peter-tanner/TREX-laser-transmit-receive-PCB/Simulation/Receiver/AAA_reverse_bias_sim.asc

C1: cap; 4.7µ
C2: cap; 10p
C3: cap; 1µ
C4: cap; 4.7µ
C5: cap; 1µ
D1: diode; MBR0530L
D2: diode; MBR0530L
D3: diode; MBR0530L
I1: current; PULSE(0 50u 1n 1n 1n 1G)
I2: current; PULSE(0 50u 1n 1n 1n 1G)
L1: ind; 10µ
R1: res; 200k
R2: res; 2Meg
U1: TPS61040_TRANS
V1: voltage; 5
Named nets: 0, -13V, +13V
.tran 1.2m
USE NORMAL
SIMULATOR
(NOT ALTERNATIVE)
50uA PD load
