peter-tanner/TREX-laser-transmit-receive-PCB/Simulation/Receiver/AAA_LMH34400_Sim.asc

C1: cap; 11p
DC_Noise: current; 5µ
PD: current; PULSE(500u 0 0 5n 5n 0 40n)
R1: res; 27k
R2: res; 5.6k
R3: res; 51
U1: TLV3601
U2: SN74LVC1G14
U4: LMH34400
V1: voltage; 3.3
V3: voltage; 3.3
Named nets: 0, Digital_OUT
.tran 0 1.5u 1u
RUN `download-copyrighted-libraries.sh`
TO DOWNLOAD SPICE MODELS BEFORE
RUNNING FIRST SIMULATION
 
AGNI
