peter-tanner/TREX-laser-transmit-receive-PCB/Simulation/Transmitter/AAA_transmitter_laser_driver_simulation.asc

C1: cap; 100n
C2: cap; 100n
C3: cap; 1µ
C4: cap; 1p
D1: LED; PT-121-B
D3: TVSdiode; SMBJ24CA
D4: TVSdiode; SMBJ24CA
Q1: npn; 2SC3356
Q2: npn; 2SC3356
R1: res; 1
R4: res; 47
R7: res; 27
R8: res; 900
R9: res; 100
U1: OPA355
U2: OPA355
U3: SN74AUC1G66
U4: SN74AUC1G66
V1: voltage; 3.3
V3: voltage; .12
V4: voltage; 3
V5: voltage; 5
V6: voltage; PULSE(3 0 0 1n 1n 9n 20n)
V7: voltage; PULSE(0 3 0 1n 1n 9n 20n)
Named nets: 0, VCC, 3V0
.tran 0 100n 0 1p
.param X=10n
.step param X list 1n 2n 5n 10n
.step param C list 10p 100p 1n 10n
Recommendation 1: Select OPA355 (OPA355UA/2K5)
* High input impedance
* High GBW (200 MegHz)
 
Recommendation 2: Use 2SC3356 NPN
* Very cheap (basic parts)
* 7GHz switching speed
* Spice model from https://pcb.mit.edu/labs/lab_03/
.model 2SC3356 NPN(IS=6E-16 NF=0.98 ISE=32E-16 NE=1.93 BF=120 
+IKF=0.0.17 VAF=10 NR=0.991 ISC=0 NC=2 BR=12 IKR=0.17 VAR=3.9 
+RB=4.16 IRB=1.96E-04 RBM=3.6 RE=0.38 RC=2  XTB=0 EG=1.11 XTI=3 
+CJE=2.8E-12 VJE=1.3 MJE=0.5 TF=15E-12 XTF=6 VTF=10 ITF=0.2 PTF=0 
+CJC=1.1E-12 VJC=0.7 MJC=0.55 XCJC=0.3 TR=1E-09 CJS=0 VJS=0.75 
+MJS=0 FC=0.5 Vceo=12 Icrating=100m mfg=cel)
Add level shifter here, use 3V max for RF transistors
No spice model for SPDT sn74auc2g53 - use two switches
careful of make before break behavior
bias
modulation
RUN `download-copyrighted-libraries.sh`
TO DOWNLOAD SPICE MODELS BEFORE
RUNNING FIRST SIMULATION
 
PETERUS
bias: 4.5mA
modulating: 7.2mA
adjust potentiometer
