peter-tanner/TREX-laser-transmit-receive-PCB/Simulation/Transmitter/AAA_transmitter_laser_driver_simulation_esd_protection.asc

C1: cap; 100n
C2: cap; 100n
C3: cap; 20p
C4: cap; 110p
C5: cap; 20p
C6: cap; 15p
C7: cap; 5p
D1: LED; PT-121-B
D3: TVSdiode; SMCJ33A
D4: TVSdiode; SMBJ24CA
L1: ind; 6n
L2: ind; 3500n
L3: FerriteBead; 1.38µ; Ipk=1 Rser=0.2 Rpar=813 Cpar=617f mfg="Würth Elektronik" pn="742792651 WE-CBF 0603"
Q1: npn; 2SC3356
Q2: npn; 2SC3356
R1: res; 330
R2: res; 120
R3: res; 36
R4: res; 47
R5: res; 36
R7: res; 27
R8: res; 90
R9: res; 10
R11: res; 100
S1: sw; SW1
U1: OPA355
U2: OPA355
V1: voltage; 3.3
V3: voltage; .12
V4: voltage; 3
V5: voltage; 5
V6: voltage; PWL(0 0 10E-9 0 10.01E-9 1)
V7: voltage; PULSE(0 3 0 1n 1n 9n 20n)
Named nets: 0, VCC, 3V0, ESD_OUT, ESD_CAP, ESD_SW
.tran 150n
Recommendation 1: Select OPA355 (OPA355UA/2K5)
* High input impedance
* High GBW (200 MegHz)
 
Recommendation 2: Use 2SC3356 NPN
* Very cheap (basic parts)
* 7GHz switching speed
* Spice model from https://pcb.mit.edu/labs/lab_03/
.model 2SC3356 NPN(IS=6E-16 NF=0.98 ISE=32E-16 NE=1.93 BF=120 
+IKF=0.0.17 VAF=10 NR=0.991 ISC=0 NC=2 BR=12 IKR=0.17 VAR=3.9 
+RB=4.16 IRB=1.96E-04 RBM=3.6 RE=0.38 RC=2  XTB=0 EG=1.11 XTI=3 
+CJE=2.8E-12 VJE=1.3 MJE=0.5 TF=15E-12 XTF=6 VTF=10 ITF=0.2 PTF=0 
+CJC=1.1E-12 VJC=0.7 MJC=0.55 XCJC=0.3 TR=1E-09 CJS=0 VJS=0.75 
+MJS=0 FC=0.5 Vceo=12 Icrating=100m mfg=cel)
analog switches shouldn't be affected
by ESD transient this far back
.model SW1 SW(Ron=0.01 Roff=10E11)
.ic V(ESD_CAP)=4000
4kV machine model
RUN `download-copyrighted-libraries.sh`
TO DOWNLOAD SPICE MODELS BEFORE
RUNNING FIRST SIMULATION
 
WON CHEN
