peter-tanner/TREX-laser-transmit-receive-PCB/Simulation/Transmitter/sweep_bias_demo.asc

C3: cap; 100n
Q2: npn; 2SC3356
R7: res; {10000*(1-a)}
R8: res; {10000*a}
R9: res; 75k
R11: res; 100
U2: OPA355
V3: voltage; 3
V4: voltage; 2.7
V5: voltage; 5
Named nets: 0, 3V0
.model 2SC3356 NPN(IS=6E-16 NF=0.98 ISE=32E-16 NE=1.93 BF=120 
+IKF=0.0.17 VAF=10 NR=0.991 ISC=0 NC=2 BR=12 IKR=0.17 VAR=3.9 
+RB=4.16 IRB=1.96E-04 RBM=3.6 RE=0.38 RC=2  XTB=0 EG=1.11 XTI=3 
+CJE=2.8E-12 VJE=1.3 MJE=0.5 TF=15E-12 XTF=6 VTF=10 ITF=0.2 PTF=0 
+CJC=1.1E-12 VJC=0.7 MJC=0.55 XCJC=0.3 TR=1E-09 CJS=0 VJS=0.75 
+MJS=0 FC=0.5 Vceo=12 Icrating=100m mfg=cel)
.step param a 1n 0.9999 .1
.op
.op
.step param R 80k 180k 10k
