peter-tanner/TREX-laser-transmit-receive-PCB/Simulation/Transmitter/trans_gate_demo.asc

C1: cap; 1µ
R1: res; 1k
R2: res; 1k
R3: res; 9k
U1: SN74AUC1G66
V1: voltage; 3.3
V3: voltage; PULSE(0 3.3 0 1n 1n 9n 20n)
Named nets: 0
.tran 0 100n 0 1p
